Pytonballoon810/Smart-Home-Zisternen-Pegelmessung/hardware/output/cistern-level-interface-3d-top.png

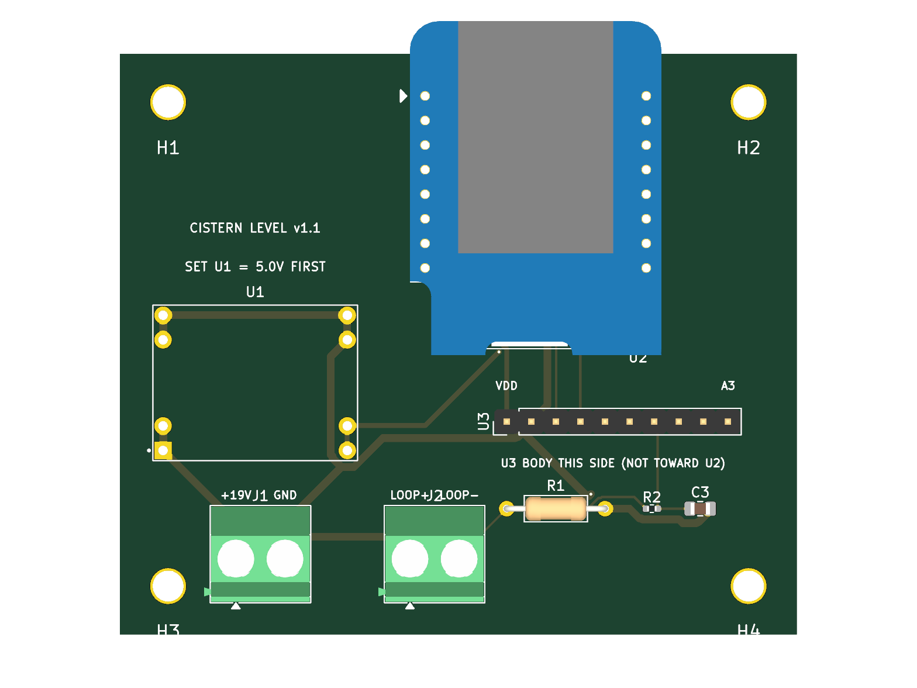
hardware/output/cistern-level-interface-3d-top.png
